UzixLS/zx-sizif-512/images/revA.small.webp

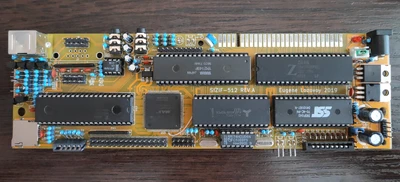
images/revA.small.webp
