UzixLS/zx-sizif-512/images/revC.jpg

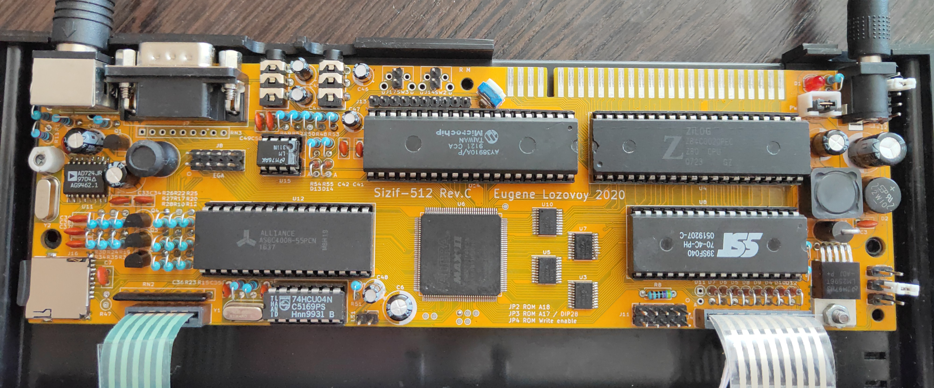
images/revC.jpg
