UzixLS/zx-sizif-512/out/pcb3d.rev.A.png

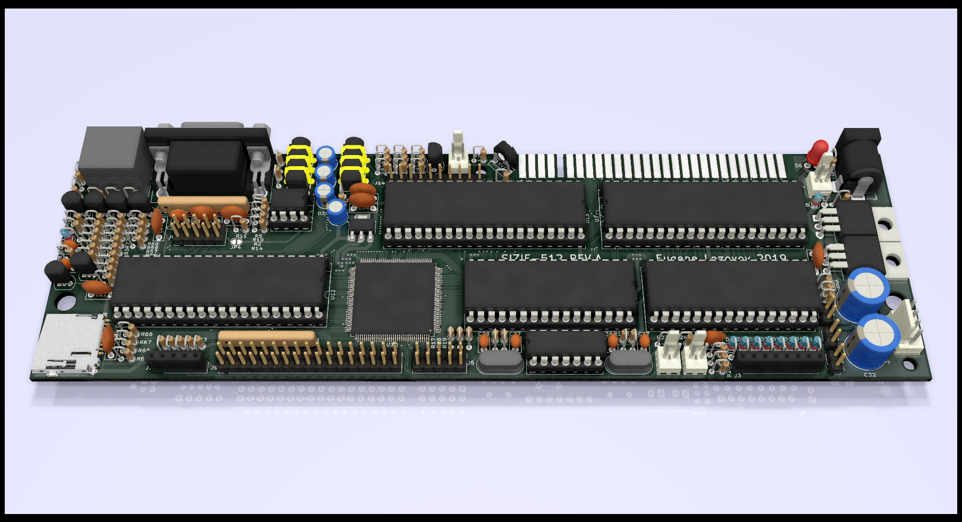
out/pcb3d.rev.A.png
