UzixLS/zx-sizif-512/out/pcb3d.rev.E1.png

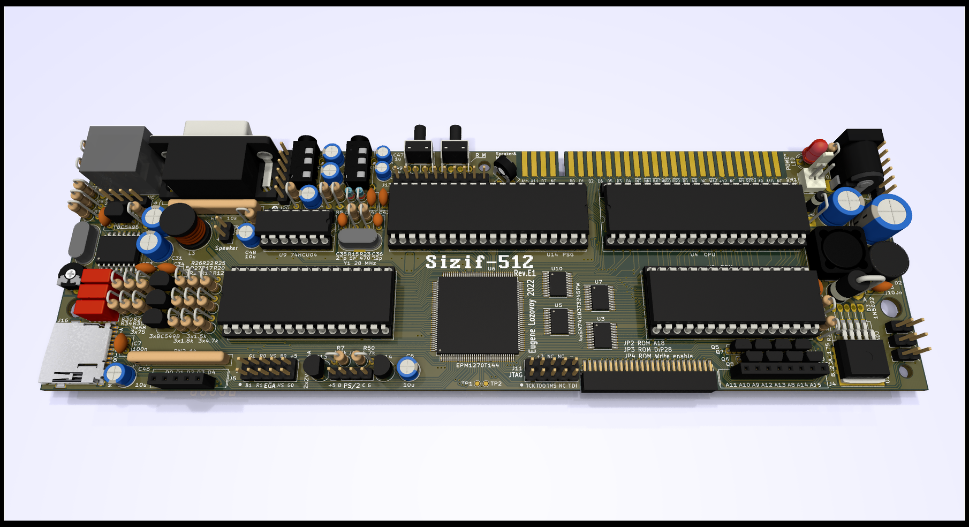
out/pcb3d.rev.E1.png
