UzixLS/zx-sizif-512/cpld/tb/az80/alu.v

//----------------------------------------------------------------------------
//  A-Z80 CPU Copyright (C) 2014,2016  Goran Devic, www.baltazarstudios.com
//
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
// PROGRAM		"Quartus II 64-Bit"
// VERSION		"Version 13.0.1 Build 232 06/12/2013 Service Pack 1 SJ Web Edition"
// CREATED		"Fri Nov 07 19:44:45 2014"

module alu(
	alu_core_R,
	alu_core_V,
	alu_core_S,
	alu_bs_oe,
	alu_parity_in,
	alu_oe,
	alu_shift_oe,
	alu_core_cf_in,
	alu_op2_oe,
	alu_op1_oe,
	alu_res_oe,
	alu_op1_sel_low,
	alu_op1_sel_zero,
	alu_op1_sel_bus,
	alu_op2_sel_zero,
	alu_op2_sel_bus,
	alu_op2_sel_lq,
	alu_op_low,
	alu_shift_in,
	alu_sel_op2_neg,
	alu_sel_op2_high,
	alu_shift_left,
	alu_shift_right,
	clk,
	bsel,
	alu_zero,
	alu_parity_out,
	alu_high_eq_9,
	alu_high_gt_9,
	alu_low_gt_9,
	alu_shift_db0,
	alu_shift_db7,
	alu_core_cf_out,
	alu_sf_out,
	alu_yf_out,
	alu_xf_out,
	alu_vf_out,
	db,
	test_db_high,
	test_db_low
);


input wire	alu_core_R;
input wire	alu_core_V;
input wire	alu_core_S;
input wire	alu_bs_oe;
input wire	alu_parity_in;
input wire	alu_oe;
input wire	alu_shift_oe;
input wire	alu_core_cf_in;
input wire	alu_op2_oe;
input wire	alu_op1_oe;
input wire	alu_res_oe;
input wire	alu_op1_sel_low;
input wire	alu_op1_sel_zero;
input wire	alu_op1_sel_bus;
input wire	alu_op2_sel_zero;
input wire	alu_op2_sel_bus;
input wire	alu_op2_sel_lq;
input wire	alu_op_low;
input wire	alu_shift_in;
input wire	alu_sel_op2_neg;
input wire	alu_sel_op2_high;
input wire	alu_shift_left;
input wire	alu_shift_right;
input wire	clk;
input wire	[2:0] bsel;
output wire	alu_zero;
output wire	alu_parity_out;
output wire	alu_high_eq_9;
output wire	alu_high_gt_9;
output wire	alu_low_gt_9;
output wire	alu_shift_db0;
output wire	alu_shift_db7;
output wire	alu_core_cf_out;
output wire	alu_sf_out;
output wire	alu_yf_out;
output wire	alu_xf_out;
output wire	alu_vf_out;
inout wire	[7:0] db;
output wire	[3:0] test_db_high;
output wire	[3:0] test_db_low;

wire	[3:0] alu_op1;
wire	[3:0] alu_op2;
wire	[3:0] db_high;
wire	[3:0] db_low;
reg	[3:0] op1_high;
reg	[3:0] op1_low;
reg	[3:0] op2_high;
reg	[3:0] op2_low;
wire	[3:0] result_hi;
reg	[3:0] result_lo;
wire	[3:0] SYNTHESIZED_WIRE_0;
wire	[3:0] SYNTHESIZED_WIRE_1;
wire	[3:0] SYNTHESIZED_WIRE_2;
wire	[3:0] SYNTHESIZED_WIRE_3;
wire	SYNTHESIZED_WIRE_35;
wire	[3:0] SYNTHESIZED_WIRE_5;
wire	[3:0] SYNTHESIZED_WIRE_7;
wire	[3:0] SYNTHESIZED_WIRE_8;
wire	SYNTHESIZED_WIRE_9;
wire	[3:0] SYNTHESIZED_WIRE_10;
wire	[3:0] SYNTHESIZED_WIRE_11;
wire	[3:0] SYNTHESIZED_WIRE_12;
wire	[3:0] SYNTHESIZED_WIRE_13;
wire	[3:0] SYNTHESIZED_WIRE_14;
wire	[3:0] SYNTHESIZED_WIRE_15;
wire	[3:0] SYNTHESIZED_WIRE_16;
wire	SYNTHESIZED_WIRE_17;
wire	[3:0] SYNTHESIZED_WIRE_18;
wire	SYNTHESIZED_WIRE_36;
wire	SYNTHESIZED_WIRE_20;
wire	[3:0] SYNTHESIZED_WIRE_21;
wire	SYNTHESIZED_WIRE_23;
wire	[3:0] SYNTHESIZED_WIRE_24;
wire	SYNTHESIZED_WIRE_37;
wire	SYNTHESIZED_WIRE_26;
wire	[3:0] SYNTHESIZED_WIRE_27;
wire	SYNTHESIZED_WIRE_29;
wire	SYNTHESIZED_WIRE_30;
wire	SYNTHESIZED_WIRE_31;
wire	SYNTHESIZED_WIRE_32;
wire	[3:0] SYNTHESIZED_WIRE_33;
wire	[3:0] SYNTHESIZED_WIRE_34;




assign	db_low[3] = alu_bs_oe ? SYNTHESIZED_WIRE_0[3] : 1'bz;
assign	db_low[2] = alu_bs_oe ? SYNTHESIZED_WIRE_0[2] : 1'bz;
assign	db_low[1] = alu_bs_oe ? SYNTHESIZED_WIRE_0[1] : 1'bz;
assign	db_low[0] = alu_bs_oe ? SYNTHESIZED_WIRE_0[0] : 1'bz;

assign	db_high[3] = alu_bs_oe ? SYNTHESIZED_WIRE_1[3] : 1'bz;
assign	db_high[2] = alu_bs_oe ? SYNTHESIZED_WIRE_1[2] : 1'bz;
assign	db_high[1] = alu_bs_oe ? SYNTHESIZED_WIRE_1[1] : 1'bz;
assign	db_high[0] = alu_bs_oe ? SYNTHESIZED_WIRE_1[0] : 1'bz;


alu_core	b2v_core(
	.cy_in(alu_core_cf_in),
	.S(alu_core_S),
	.V(alu_core_V),
	.R(alu_core_R),
	.op1(alu_op1),
	.op2(alu_op2),
	.cy_out(alu_core_cf_out),
	.vf_out(alu_vf_out),
	.result(result_hi));

assign	db[3] = alu_oe ? db_low[3] : 1'bz;
assign	db[2] = alu_oe ? db_low[2] : 1'bz;
assign	db[1] = alu_oe ? db_low[1] : 1'bz;
assign	db[0] = alu_oe ? db_low[0] : 1'bz;

assign	db[7] = alu_oe ? db_high[3] : 1'bz;
assign	db[6] = alu_oe ? db_high[2] : 1'bz;
assign	db[5] = alu_oe ? db_high[1] : 1'bz;
assign	db[4] = alu_oe ? db_high[0] : 1'bz;


alu_bit_select	b2v_input_bit_select(
	.bsel(bsel),
	.bs_out_high(SYNTHESIZED_WIRE_1),
	.bs_out_low(SYNTHESIZED_WIRE_0));


alu_shifter_core	b2v_input_shift(
	.shift_in(alu_shift_in),
	.shift_left(alu_shift_left),
	.shift_right(alu_shift_right),
	.db(db),
	.shift_db0(alu_shift_db0),
	.shift_db7(alu_shift_db7),
	.out_high(SYNTHESIZED_WIRE_34),
	.out_low(SYNTHESIZED_WIRE_33));


always@(posedge clk)
begin
if (alu_op_low)
	begin
	result_lo[3:0] <= result_hi[3:0];
	end
end

assign	alu_op1 = SYNTHESIZED_WIRE_2 | SYNTHESIZED_WIRE_3;

assign	SYNTHESIZED_WIRE_17 =  ~alu_op_low;

assign	db_low[3] = alu_op2_oe ? op2_low[3] : 1'bz;
assign	db_low[2] = alu_op2_oe ? op2_low[2] : 1'bz;
assign	db_low[1] = alu_op2_oe ? op2_low[1] : 1'bz;
assign	db_low[0] = alu_op2_oe ? op2_low[0] : 1'bz;

assign	db_high[3] = alu_op2_oe ? op2_high[3] : 1'bz;
assign	db_high[2] = alu_op2_oe ? op2_high[2] : 1'bz;
assign	db_high[1] = alu_op2_oe ? op2_high[1] : 1'bz;
assign	db_high[0] = alu_op2_oe ? op2_high[0] : 1'bz;

assign	SYNTHESIZED_WIRE_5 =  ~op2_low;

assign	SYNTHESIZED_WIRE_7 =  ~op2_high;

assign	SYNTHESIZED_WIRE_12 = op2_low & {SYNTHESIZED_WIRE_35,SYNTHESIZED_WIRE_35,SYNTHESIZED_WIRE_35,SYNTHESIZED_WIRE_35};

assign	SYNTHESIZED_WIRE_11 = {alu_sel_op2_neg,alu_sel_op2_neg,alu_sel_op2_neg,alu_sel_op2_neg} & SYNTHESIZED_WIRE_5;

assign	SYNTHESIZED_WIRE_14 = op2_high & {SYNTHESIZED_WIRE_35,SYNTHESIZED_WIRE_35,SYNTHESIZED_WIRE_35,SYNTHESIZED_WIRE_35};

assign	SYNTHESIZED_WIRE_13 = {alu_sel_op2_neg,alu_sel_op2_neg,alu_sel_op2_neg,alu_sel_op2_neg} & SYNTHESIZED_WIRE_7;

assign	SYNTHESIZED_WIRE_16 = SYNTHESIZED_WIRE_8 & {SYNTHESIZED_WIRE_9,SYNTHESIZED_WIRE_9,SYNTHESIZED_WIRE_9,SYNTHESIZED_WIRE_9};

assign	SYNTHESIZED_WIRE_15 = {alu_sel_op2_high,alu_sel_op2_high,alu_sel_op2_high,alu_sel_op2_high} & SYNTHESIZED_WIRE_10;

assign	SYNTHESIZED_WIRE_8 = SYNTHESIZED_WIRE_11 | SYNTHESIZED_WIRE_12;

assign	SYNTHESIZED_WIRE_10 = SYNTHESIZED_WIRE_13 | SYNTHESIZED_WIRE_14;

assign	alu_op2 = SYNTHESIZED_WIRE_15 | SYNTHESIZED_WIRE_16;

assign	SYNTHESIZED_WIRE_35 =  ~alu_sel_op2_neg;

assign	SYNTHESIZED_WIRE_9 =  ~alu_sel_op2_high;

assign	db_low[3] = alu_res_oe ? result_lo[3] : 1'bz;
assign	db_low[2] = alu_res_oe ? result_lo[2] : 1'bz;
assign	db_low[1] = alu_res_oe ? result_lo[1] : 1'bz;
assign	db_low[0] = alu_res_oe ? result_lo[0] : 1'bz;

assign	db_high[3] = alu_res_oe ? result_hi[3] : 1'bz;
assign	db_high[2] = alu_res_oe ? result_hi[2] : 1'bz;
assign	db_high[1] = alu_res_oe ? result_hi[1] : 1'bz;
assign	db_high[0] = alu_res_oe ? result_hi[0] : 1'bz;

assign	SYNTHESIZED_WIRE_3 = op1_low & {alu_op_low,alu_op_low,alu_op_low,alu_op_low};

assign	SYNTHESIZED_WIRE_2 = {SYNTHESIZED_WIRE_17,SYNTHESIZED_WIRE_17,SYNTHESIZED_WIRE_17,SYNTHESIZED_WIRE_17} & op1_high;


always@(posedge SYNTHESIZED_WIRE_36)
begin
if (SYNTHESIZED_WIRE_20)
	begin
	op1_high[3:0] <= SYNTHESIZED_WIRE_18[3:0];
	end
end


always@(posedge SYNTHESIZED_WIRE_36)
begin
if (SYNTHESIZED_WIRE_23)
	begin
	op1_low[3:0] <= SYNTHESIZED_WIRE_21[3:0];
	end
end


always@(posedge SYNTHESIZED_WIRE_37)
begin
if (SYNTHESIZED_WIRE_26)
	begin
	op2_high[3:0] <= SYNTHESIZED_WIRE_24[3:0];
	end
end


always@(posedge SYNTHESIZED_WIRE_37)
begin
if (SYNTHESIZED_WIRE_29)
	begin
	op2_low[3:0] <= SYNTHESIZED_WIRE_27[3:0];
	end
end

assign	db_low[3] = alu_op1_oe ? op1_low[3] : 1'bz;
assign	db_low[2] = alu_op1_oe ? op1_low[2] : 1'bz;
assign	db_low[1] = alu_op1_oe ? op1_low[1] : 1'bz;
assign	db_low[0] = alu_op1_oe ? op1_low[0] : 1'bz;

assign	db_high[3] = alu_op1_oe ? op1_high[3] : 1'bz;
assign	db_high[2] = alu_op1_oe ? op1_high[2] : 1'bz;
assign	db_high[1] = alu_op1_oe ? op1_high[1] : 1'bz;
assign	db_high[0] = alu_op1_oe ? op1_high[0] : 1'bz;

assign	SYNTHESIZED_WIRE_36 =  ~clk;

assign	SYNTHESIZED_WIRE_37 =  ~clk;


alu_mux_2z	b2v_op1_latch_mux_high(
	.sel_a(alu_op1_sel_bus),
	.sel_zero(alu_op1_sel_zero),
	.a(db_high),
	.ena(SYNTHESIZED_WIRE_20),
	.Q(SYNTHESIZED_WIRE_18));


alu_mux_3z	b2v_op1_latch_mux_low(
	.sel_a(alu_op1_sel_bus),
	.sel_b(alu_op1_sel_low),
	.sel_zero(alu_op1_sel_zero),
	.a(db_low),
	.b(db_high),
	.ena(SYNTHESIZED_WIRE_23),
	.Q(SYNTHESIZED_WIRE_21));


alu_mux_3z	b2v_op2_latch_mux_high(
	.sel_a(alu_op2_sel_bus),
	.sel_b(alu_op2_sel_lq),
	.sel_zero(alu_op2_sel_zero),
	.a(db_high),
	.b(db_low),
	.ena(SYNTHESIZED_WIRE_26),
	.Q(SYNTHESIZED_WIRE_24));


alu_mux_3z	b2v_op2_latch_mux_low(
	.sel_a(alu_op2_sel_bus),
	.sel_b(alu_op2_sel_lq),
	.sel_zero(alu_op2_sel_zero),
	.a(db_low),
	.b(alu_op1),
	.ena(SYNTHESIZED_WIRE_29),
	.Q(SYNTHESIZED_WIRE_27));

assign	alu_parity_out = SYNTHESIZED_WIRE_30 ^ result_hi[0];

assign	SYNTHESIZED_WIRE_30 = SYNTHESIZED_WIRE_31 ^ result_hi[1];

assign	SYNTHESIZED_WIRE_31 = SYNTHESIZED_WIRE_32 ^ result_hi[2];

assign	SYNTHESIZED_WIRE_32 = alu_parity_in ^ result_hi[3];


alu_prep_daa	b2v_prep_daa(
	.high(op1_high),
	.low(op1_low),
	.low_gt_9(alu_low_gt_9),
	.high_gt_9(alu_high_gt_9),
	.high_eq_9(alu_high_eq_9));

assign	db_low[3] = alu_shift_oe ? SYNTHESIZED_WIRE_33[3] : 1'bz;
assign	db_low[2] = alu_shift_oe ? SYNTHESIZED_WIRE_33[2] : 1'bz;
assign	db_low[1] = alu_shift_oe ? SYNTHESIZED_WIRE_33[1] : 1'bz;
assign	db_low[0] = alu_shift_oe ? SYNTHESIZED_WIRE_33[0] : 1'bz;

assign	db_high[3] = alu_shift_oe ? SYNTHESIZED_WIRE_34[3] : 1'bz;
assign	db_high[2] = alu_shift_oe ? SYNTHESIZED_WIRE_34[2] : 1'bz;
assign	db_high[1] = alu_shift_oe ? SYNTHESIZED_WIRE_34[1] : 1'bz;
assign	db_high[0] = alu_shift_oe ? SYNTHESIZED_WIRE_34[0] : 1'bz;

assign	alu_zero = ~(db_low[2] | db_low[1] | db_low[3] | db_high[1] | db_high[0] | db_high[2] | db_low[0] | db_high[3]);

assign	alu_sf_out = db_high[3];
assign	alu_yf_out = db_high[1];
assign	alu_xf_out = db_low[3];
assign	test_db_high = db_high;
assign	test_db_low = db_low;

endmodule
