UzixLS/zx-sizif-512/cpld/tb/az80/alu_flags.v

//----------------------------------------------------------------------------
//  A-Z80 CPU Copyright (C) 2014,2016  Goran Devic, www.baltazarstudios.com
//
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
// PROGRAM		"Quartus II 64-Bit"
// VERSION		"Version 13.0.1 Build 232 06/12/2013 Service Pack 1 SJ Web Edition"
// CREATED		"Sat Dec 10 09:01:30 2016"

module alu_flags(
	ctl_flags_oe,
	ctl_flags_bus,
	ctl_flags_alu,
	alu_sf_out,
	alu_yf_out,
	alu_xf_out,
	ctl_flags_nf_set,
	alu_zero,
	shift_cf_out,
	alu_core_cf_out,
	daa_cf_out,
	ctl_flags_cf_set,
	ctl_flags_cf_cpl,
	pf_sel,
	ctl_flags_cf_we,
	ctl_flags_sz_we,
	ctl_flags_xy_we,
	ctl_flags_hf_we,
	ctl_flags_pf_we,
	ctl_flags_nf_we,
	ctl_flags_cf2_we,
	ctl_flags_hf_cpl,
	ctl_flags_use_cf2,
	ctl_flags_hf2_we,
	ctl_flags_nf_clr,
	ctl_alu_zero_16bit,
	clk,
	ctl_flags_cf2_sel_shift,
	ctl_flags_cf2_sel_daa,
	nhold_clk_wait,
	flags_sf,
	flags_zf,
	flags_hf,
	flags_pf,
	flags_cf,
	flags_nf,
	flags_cf_latch,
	flags_hf2,
	db
);


input wire	ctl_flags_oe;
input wire	ctl_flags_bus;
input wire	ctl_flags_alu;
input wire	alu_sf_out;
input wire	alu_yf_out;
input wire	alu_xf_out;
input wire	ctl_flags_nf_set;
input wire	alu_zero;
input wire	shift_cf_out;
input wire	alu_core_cf_out;
input wire	daa_cf_out;
input wire	ctl_flags_cf_set;
input wire	ctl_flags_cf_cpl;
input wire	pf_sel;
input wire	ctl_flags_cf_we;
input wire	ctl_flags_sz_we;
input wire	ctl_flags_xy_we;
input wire	ctl_flags_hf_we;
input wire	ctl_flags_pf_we;
input wire	ctl_flags_nf_we;
input wire	ctl_flags_cf2_we;
input wire	ctl_flags_hf_cpl;
input wire	ctl_flags_use_cf2;
input wire	ctl_flags_hf2_we;
input wire	ctl_flags_nf_clr;
input wire	ctl_alu_zero_16bit;
input wire	clk;
input wire	ctl_flags_cf2_sel_shift;
input wire	ctl_flags_cf2_sel_daa;
input wire	nhold_clk_wait;
output wire	flags_sf;
output wire	flags_zf;
output wire	flags_hf;
output wire	flags_pf;
output wire	flags_cf;
output wire	flags_nf;
output wire	flags_cf_latch;
output reg	flags_hf2;
inout wire	[7:0] db;

reg	flags_xf;
reg	flags_yf;
wire	[1:0] sel;
reg	DFFE_inst_latch_hf;
wire	SYNTHESIZED_WIRE_0;
wire	SYNTHESIZED_WIRE_1;
wire	SYNTHESIZED_WIRE_2;
wire	SYNTHESIZED_WIRE_3;
wire	SYNTHESIZED_WIRE_4;
wire	SYNTHESIZED_WIRE_5;
wire	SYNTHESIZED_WIRE_6;
wire	SYNTHESIZED_WIRE_7;
reg	SYNTHESIZED_WIRE_39;
wire	SYNTHESIZED_WIRE_8;
wire	SYNTHESIZED_WIRE_9;
wire	SYNTHESIZED_WIRE_10;
wire	SYNTHESIZED_WIRE_11;
wire	SYNTHESIZED_WIRE_12;
wire	SYNTHESIZED_WIRE_13;
wire	SYNTHESIZED_WIRE_14;
wire	SYNTHESIZED_WIRE_15;
wire	SYNTHESIZED_WIRE_16;
wire	SYNTHESIZED_WIRE_17;
wire	SYNTHESIZED_WIRE_18;
wire	SYNTHESIZED_WIRE_19;
wire	SYNTHESIZED_WIRE_20;
wire	SYNTHESIZED_WIRE_21;
wire	SYNTHESIZED_WIRE_22;
reg	DFFE_inst_latch_sf;
wire	SYNTHESIZED_WIRE_23;
reg	DFFE_inst_latch_pf;
reg	DFFE_inst_latch_nf;
wire	SYNTHESIZED_WIRE_24;
wire	SYNTHESIZED_WIRE_25;
wire	SYNTHESIZED_WIRE_26;
wire	SYNTHESIZED_WIRE_27;
wire	SYNTHESIZED_WIRE_28;
wire	SYNTHESIZED_WIRE_29;
wire	SYNTHESIZED_WIRE_40;
wire	SYNTHESIZED_WIRE_32;
wire	SYNTHESIZED_WIRE_33;
wire	SYNTHESIZED_WIRE_34;
wire	SYNTHESIZED_WIRE_35;
wire	SYNTHESIZED_WIRE_36;
wire	SYNTHESIZED_WIRE_37;
reg	DFFE_inst_latch_cf;
reg	DFFE_inst_latch_cf2;
wire	SYNTHESIZED_WIRE_38;

assign	flags_sf = DFFE_inst_latch_sf;
assign	flags_zf = SYNTHESIZED_WIRE_39;
assign	flags_hf = SYNTHESIZED_WIRE_23;
assign	flags_pf = DFFE_inst_latch_pf;
assign	flags_cf = SYNTHESIZED_WIRE_24;
assign	flags_nf = DFFE_inst_latch_nf;
assign	flags_cf_latch = DFFE_inst_latch_cf;
assign	SYNTHESIZED_WIRE_38 = 0;



assign	SYNTHESIZED_WIRE_10 = db[7] & ctl_flags_bus;

assign	SYNTHESIZED_WIRE_17 = alu_xf_out & ctl_flags_alu;

assign	SYNTHESIZED_WIRE_20 = db[2] & ctl_flags_bus;

assign	SYNTHESIZED_WIRE_19 = pf_sel & ctl_flags_alu;

assign	SYNTHESIZED_WIRE_2 = db[1] & ctl_flags_bus;

assign	SYNTHESIZED_WIRE_23 = DFFE_inst_latch_hf ^ ctl_flags_hf_cpl;

assign	SYNTHESIZED_WIRE_22 = db[0] & ctl_flags_bus;

assign	SYNTHESIZED_WIRE_21 = ctl_flags_alu & alu_core_cf_out;

assign	SYNTHESIZED_WIRE_8 =  ~ctl_flags_cf2_we;

assign	SYNTHESIZED_WIRE_24 = SYNTHESIZED_WIRE_0 ^ ctl_flags_cf_cpl;

assign	SYNTHESIZED_WIRE_1 = alu_sf_out & ctl_flags_alu;

assign	SYNTHESIZED_WIRE_9 = alu_sf_out & ctl_flags_alu;

assign	SYNTHESIZED_WIRE_5 = ctl_flags_nf_set | SYNTHESIZED_WIRE_1 | SYNTHESIZED_WIRE_2;

assign	SYNTHESIZED_WIRE_37 = SYNTHESIZED_WIRE_3 & SYNTHESIZED_WIRE_4;


assign	SYNTHESIZED_WIRE_32 = SYNTHESIZED_WIRE_5 & SYNTHESIZED_WIRE_6;

assign	SYNTHESIZED_WIRE_6 =  ~ctl_flags_nf_clr;

assign	SYNTHESIZED_WIRE_7 =  ~ctl_alu_zero_16bit;

assign	SYNTHESIZED_WIRE_4 = SYNTHESIZED_WIRE_7 | SYNTHESIZED_WIRE_39;

assign	SYNTHESIZED_WIRE_27 = ctl_flags_cf_we & nhold_clk_wait & SYNTHESIZED_WIRE_8;

assign	SYNTHESIZED_WIRE_29 = ctl_flags_cf2_we & nhold_clk_wait;

assign	SYNTHESIZED_WIRE_12 = db[6] & ctl_flags_bus;

assign	SYNTHESIZED_WIRE_34 = SYNTHESIZED_WIRE_9 | SYNTHESIZED_WIRE_10;

assign	SYNTHESIZED_WIRE_3 = SYNTHESIZED_WIRE_11 | SYNTHESIZED_WIRE_12;

assign	SYNTHESIZED_WIRE_36 = SYNTHESIZED_WIRE_13 | SYNTHESIZED_WIRE_14;

assign	SYNTHESIZED_WIRE_40 = SYNTHESIZED_WIRE_15 | SYNTHESIZED_WIRE_16;

assign	SYNTHESIZED_WIRE_35 = SYNTHESIZED_WIRE_17 | SYNTHESIZED_WIRE_18;

assign	SYNTHESIZED_WIRE_33 = SYNTHESIZED_WIRE_19 | SYNTHESIZED_WIRE_20;

assign	SYNTHESIZED_WIRE_11 = alu_zero & ctl_flags_alu;

assign	SYNTHESIZED_WIRE_26 = SYNTHESIZED_WIRE_21 | SYNTHESIZED_WIRE_22;

assign	db[7] = ctl_flags_oe ? DFFE_inst_latch_sf : 1'bz;

assign	SYNTHESIZED_WIRE_14 = db[5] & ctl_flags_bus;

assign	db[6] = ctl_flags_oe ? SYNTHESIZED_WIRE_39 : 1'bz;

assign	db[5] = ctl_flags_oe ? flags_yf : 1'bz;

assign	db[4] = ctl_flags_oe ? SYNTHESIZED_WIRE_23 : 1'bz;

assign	db[3] = ctl_flags_oe ? flags_xf : 1'bz;

assign	db[2] = ctl_flags_oe ? DFFE_inst_latch_pf : 1'bz;

assign	db[1] = ctl_flags_oe ? DFFE_inst_latch_nf : 1'bz;

assign	db[0] = ctl_flags_oe ? SYNTHESIZED_WIRE_24 : 1'bz;

assign	SYNTHESIZED_WIRE_13 = alu_yf_out & ctl_flags_alu;

assign	SYNTHESIZED_WIRE_0 = ctl_flags_cf_set | SYNTHESIZED_WIRE_25;

assign	SYNTHESIZED_WIRE_16 = db[4] & ctl_flags_bus;

assign	SYNTHESIZED_WIRE_15 = alu_core_cf_out & ctl_flags_alu;

assign	SYNTHESIZED_WIRE_18 = db[3] & ctl_flags_bus;


always@(posedge clk)
begin
if (SYNTHESIZED_WIRE_27)
	begin
	DFFE_inst_latch_cf <= SYNTHESIZED_WIRE_26;
	end
end


always@(posedge clk)
begin
if (SYNTHESIZED_WIRE_29)
	begin
	DFFE_inst_latch_cf2 <= SYNTHESIZED_WIRE_28;
	end
end


always@(posedge clk)
begin
if (ctl_flags_hf_we)
	begin
	DFFE_inst_latch_hf <= SYNTHESIZED_WIRE_40;
	end
end


always@(posedge clk)
begin
if (ctl_flags_hf2_we)
	begin
	flags_hf2 <= SYNTHESIZED_WIRE_40;
	end
end


always@(posedge clk)
begin
if (ctl_flags_nf_we)
	begin
	DFFE_inst_latch_nf <= SYNTHESIZED_WIRE_32;
	end
end


always@(posedge clk)
begin
if (ctl_flags_pf_we)
	begin
	DFFE_inst_latch_pf <= SYNTHESIZED_WIRE_33;
	end
end


always@(posedge clk)
begin
if (ctl_flags_sz_we)
	begin
	DFFE_inst_latch_sf <= SYNTHESIZED_WIRE_34;
	end
end


always@(posedge clk)
begin
if (ctl_flags_xy_we)
	begin
	flags_xf <= SYNTHESIZED_WIRE_35;
	end
end


always@(posedge clk)
begin
if (ctl_flags_xy_we)
	begin
	flags_yf <= SYNTHESIZED_WIRE_36;
	end
end


always@(posedge clk)
begin
if (ctl_flags_sz_we)
	begin
	SYNTHESIZED_WIRE_39 <= SYNTHESIZED_WIRE_37;
	end
end


alu_mux_2	b2v_inst_mux_cf(
	.in0(DFFE_inst_latch_cf),
	.in1(DFFE_inst_latch_cf2),
	.sel1(ctl_flags_use_cf2),
	.out(SYNTHESIZED_WIRE_25));


alu_mux_4	b2v_inst_mux_cf2(
	.in0(alu_core_cf_out),
	.in1(shift_cf_out),
	.in2(daa_cf_out),
	.in3(SYNTHESIZED_WIRE_38),
	.sel(sel),
	.out(SYNTHESIZED_WIRE_28));

assign	sel[0] = ctl_flags_cf2_sel_shift;
assign	sel[1] = ctl_flags_cf2_sel_daa;

endmodule
