UzixLS/zx-sizif-512/cpld/tb/az80/address_latch.v

//----------------------------------------------------------------------------
//  A-Z80 CPU Copyright (C) 2014,2016  Goran Devic, www.baltazarstudios.com
//
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
// PROGRAM		"Quartus II 64-Bit"
// VERSION		"Version 13.0.1 Build 232 06/12/2013 Service Pack 1 SJ Web Edition"
// CREATED		"Sat Feb 27 08:13:14 2016"

module address_latch(
	ctl_inc_cy,
	ctl_inc_dec,
	ctl_al_we,
	ctl_inc_limit6,
	ctl_bus_inc_oe,
	clk,
	ctl_apin_mux,
	ctl_apin_mux2,
	clrpc,
	nreset,
	address_is_1,
	abus,
	address
);


input wire	ctl_inc_cy;
input wire	ctl_inc_dec;
input wire	ctl_al_we;
input wire	ctl_inc_limit6;
input wire	ctl_bus_inc_oe;
input wire	clk;
input wire	ctl_apin_mux;
input wire	ctl_apin_mux2;
input wire	clrpc;
input wire	nreset;
output wire	address_is_1;
inout wire	[15:0] abus;
output wire	[15:0] address;

wire	[15:0] abusz;
reg	[15:0] Q;
wire	SYNTHESIZED_WIRE_0;
wire	SYNTHESIZED_WIRE_1;
wire	SYNTHESIZED_WIRE_2;
wire	[15:0] SYNTHESIZED_WIRE_7;
wire	SYNTHESIZED_WIRE_4;
wire	[15:0] SYNTHESIZED_WIRE_5;





always@(posedge clk or negedge nreset)
begin
if (!nreset)
	begin
	Q[15:0] <= 16'b0000000000000000;
	end
else
if (ctl_al_we)
	begin
	Q[15:0] <= abusz[15:0];
	end
end

assign	address_is_1 = ~(SYNTHESIZED_WIRE_0 | SYNTHESIZED_WIRE_1);

assign	abusz = {SYNTHESIZED_WIRE_2,SYNTHESIZED_WIRE_2,SYNTHESIZED_WIRE_2,SYNTHESIZED_WIRE_2,SYNTHESIZED_WIRE_2,SYNTHESIZED_WIRE_2,SYNTHESIZED_WIRE_2,SYNTHESIZED_WIRE_2,SYNTHESIZED_WIRE_2,SYNTHESIZED_WIRE_2,SYNTHESIZED_WIRE_2,SYNTHESIZED_WIRE_2,SYNTHESIZED_WIRE_2,SYNTHESIZED_WIRE_2,SYNTHESIZED_WIRE_2,SYNTHESIZED_WIRE_2} & abus;

assign	abus[15] = ctl_bus_inc_oe ? SYNTHESIZED_WIRE_7[15] : 1'bz;
assign	abus[14] = ctl_bus_inc_oe ? SYNTHESIZED_WIRE_7[14] : 1'bz;
assign	abus[13] = ctl_bus_inc_oe ? SYNTHESIZED_WIRE_7[13] : 1'bz;
assign	abus[12] = ctl_bus_inc_oe ? SYNTHESIZED_WIRE_7[12] : 1'bz;
assign	abus[11] = ctl_bus_inc_oe ? SYNTHESIZED_WIRE_7[11] : 1'bz;
assign	abus[10] = ctl_bus_inc_oe ? SYNTHESIZED_WIRE_7[10] : 1'bz;
assign	abus[9] = ctl_bus_inc_oe ? SYNTHESIZED_WIRE_7[9] : 1'bz;
assign	abus[8] = ctl_bus_inc_oe ? SYNTHESIZED_WIRE_7[8] : 1'bz;
assign	abus[7] = ctl_bus_inc_oe ? SYNTHESIZED_WIRE_7[7] : 1'bz;
assign	abus[6] = ctl_bus_inc_oe ? SYNTHESIZED_WIRE_7[6] : 1'bz;
assign	abus[5] = ctl_bus_inc_oe ? SYNTHESIZED_WIRE_7[5] : 1'bz;
assign	abus[4] = ctl_bus_inc_oe ? SYNTHESIZED_WIRE_7[4] : 1'bz;
assign	abus[3] = ctl_bus_inc_oe ? SYNTHESIZED_WIRE_7[3] : 1'bz;
assign	abus[2] = ctl_bus_inc_oe ? SYNTHESIZED_WIRE_7[2] : 1'bz;
assign	abus[1] = ctl_bus_inc_oe ? SYNTHESIZED_WIRE_7[1] : 1'bz;
assign	abus[0] = ctl_bus_inc_oe ? SYNTHESIZED_WIRE_7[0] : 1'bz;

assign	SYNTHESIZED_WIRE_0 = Q[7] | Q[5] | Q[6] | Q[4] | Q[2] | Q[3] | Q[1] | SYNTHESIZED_WIRE_4;

assign	SYNTHESIZED_WIRE_1 = Q[15] | Q[13] | Q[14] | Q[12] | Q[10] | Q[11] | Q[9] | Q[8];


address_mux	b2v_inst7(
	.select(ctl_apin_mux2),
	.in0(SYNTHESIZED_WIRE_5),
	.in1(Q),
	.out(address));

assign	SYNTHESIZED_WIRE_2 =  ~clrpc;


inc_dec	b2v_inst_inc_dec(
	.limit6(ctl_inc_limit6),
	.decrement(ctl_inc_dec),
	.carry_in(ctl_inc_cy),
	.d(Q),
	.address(SYNTHESIZED_WIRE_7));


address_mux	b2v_mux(
	.select(ctl_apin_mux),
	.in0(abusz),
	.in1(SYNTHESIZED_WIRE_7),
	.out(SYNTHESIZED_WIRE_5));

assign	SYNTHESIZED_WIRE_4 =  ~Q[0];


endmodule
