UzixLS/zx-sizif-512/cpld/rtl/rgb.sv

module rgb (
    input clk28,
    input strobe,

    input up_en,
    input bright_boost,

    input [2:0] r_i,
    input [2:0] g_i,
    input [1:0] b_i,

    output reg [1:0] r_o,
    output reg [1:0] g_o,
    output reg [1:0] b_o
);


`ifdef REV_C

function [1:0] color_2to2; input [1:0] in;
    case (in)
        2'b00: color_2to2 = 2'b00; // 0mV
        2'b01: color_2to2 = 2'b10; // 343mV
        2'b10: color_2to2 = strobe? 2'b10 : 2'bz1;
        2'b11: color_2to2 = 2'b11; // 675mV
    endcase
endfunction
function [1:0] color_3to2; input [2:0] in;
    case (in)
        3'b000: color_3to2 = 2'b00; // 0mV
        3'b001: color_3to2 = strobe? 2'b00 : 2'b10;
        3'b010: color_3to2 = 2'bz1; // 237mV
        3'b011: color_3to2 = 2'b10; // 343mV
        3'b100: color_3to2 = strobe? 2'b10 : 2'bz1;
        3'b101: color_3to2 = 2'b1z; // 505mV
        3'b110: color_3to2 = strobe? 2'bz1 : 2'b1z;
        3'b111: color_3to2 = 2'b11; // 675mV
    endcase
endfunction
function [5:0] color_bright; input [5:0] in;
    color_bright = {in[5], in[4]? 1'b1 : 1'bz, 
                    in[3], in[2]? 1'b1 : 1'bz,
                    in[1], in[0]? 1'b1 : 1'bz};
endfunction

`else /* REV_C */

function [1:0] color_2to2; input [1:0] in;
    case (in)
        2'b00: color_2to2 = 2'b00;
        2'b01: color_2to2 = strobe? 2'b10 : 2'b0z;
        2'b10: color_2to2 = strobe? 2'b1z : 2'bz0;
        2'b11: color_2to2 = 2'b11;
    endcase
endfunction
function [1:0] color_3to2; input [2:0] in;
    case (in)
        3'b000: color_3to2 = 2'b00;
        3'b001: color_3to2 = strobe? 2'bz1 : 2'bzz;
        3'b010: color_3to2 = strobe? 2'b1z : 2'b00;
        3'b011: color_3to2 = strobe? 2'b11 : 2'b00;
        3'b100: color_3to2 = strobe? 2'b10 : 2'bzz;
        3'b101: color_3to2 = 2'b10;
        3'b110: color_3to2 = strobe? 2'b11 : 2'b10;
        3'b111: color_3to2 = 2'b11;
    endcase
endfunction
function [5:0] color_bright; input [5:0] in;
    color_bright = {in[5], (strobe | in[4])? in[4] : 1'bz, 
                    in[3], (strobe | in[2])? in[2] : 1'bz,
                    in[1], (strobe | in[0])? in[0] : 1'bz};
endfunction

`endif /* REV_C */


always @(posedge clk28) begin
    if (up_en) begin
        g_o = color_3to2(g_i);
        r_o = color_3to2(r_i);
        b_o = color_2to2(b_i);
    end
    else if (bright_boost) begin
        {g_o, r_o, b_o} = color_bright({g_i[2:1], r_i[2:1], b_i});
    end
    else begin
        {g_o, r_o, b_o} = {g_i[2:1], r_i[2:1], b_i};
    end
end


endmodule
